lkunelk/hopping-eggplant/hardware/results/sample_sim.png

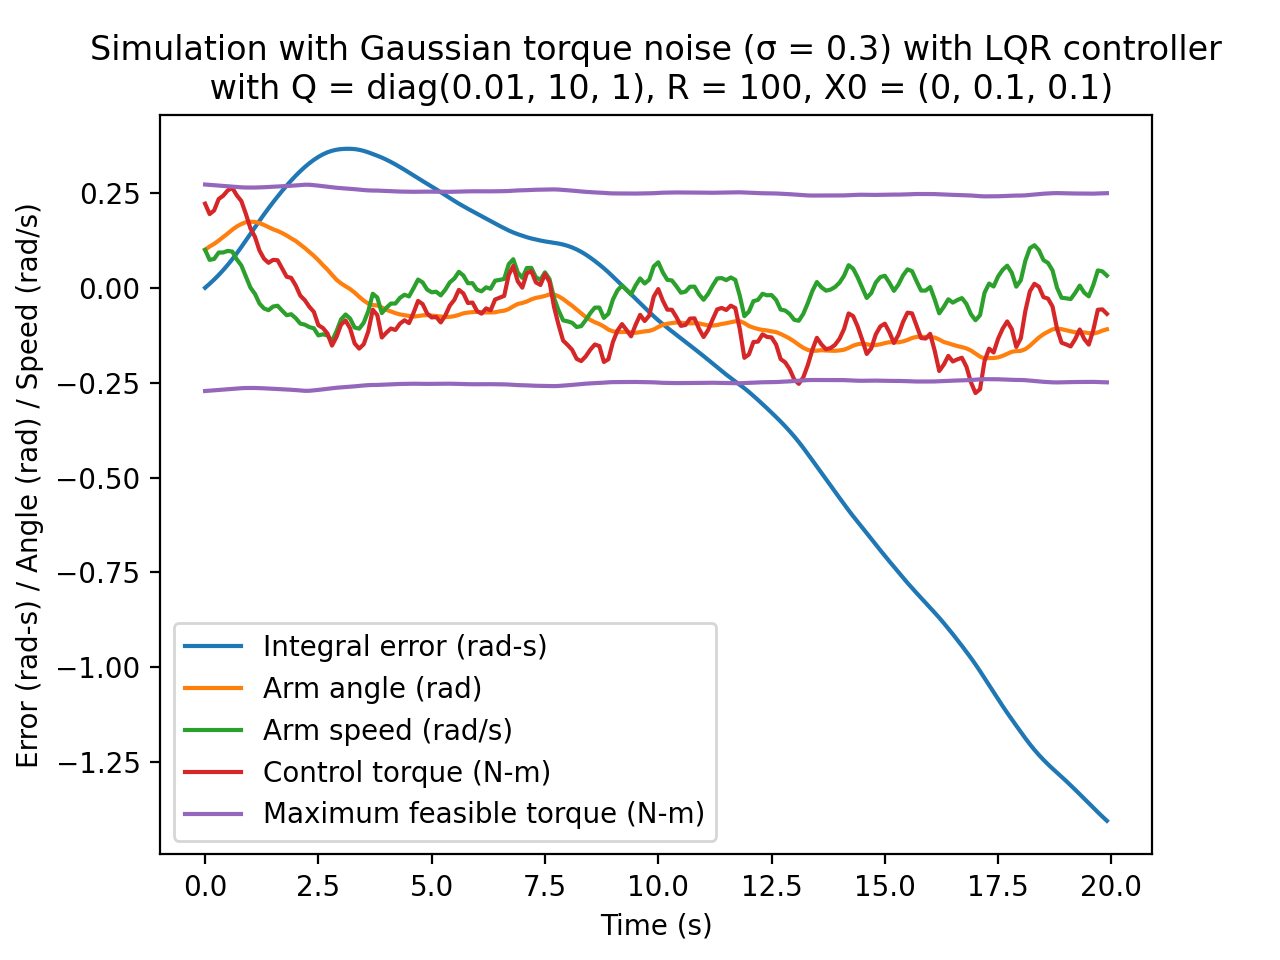
hardware/results/sample_sim.png
