lkunelk/hopping-eggplant/hardware/results/sample_sim_0p1sig.png

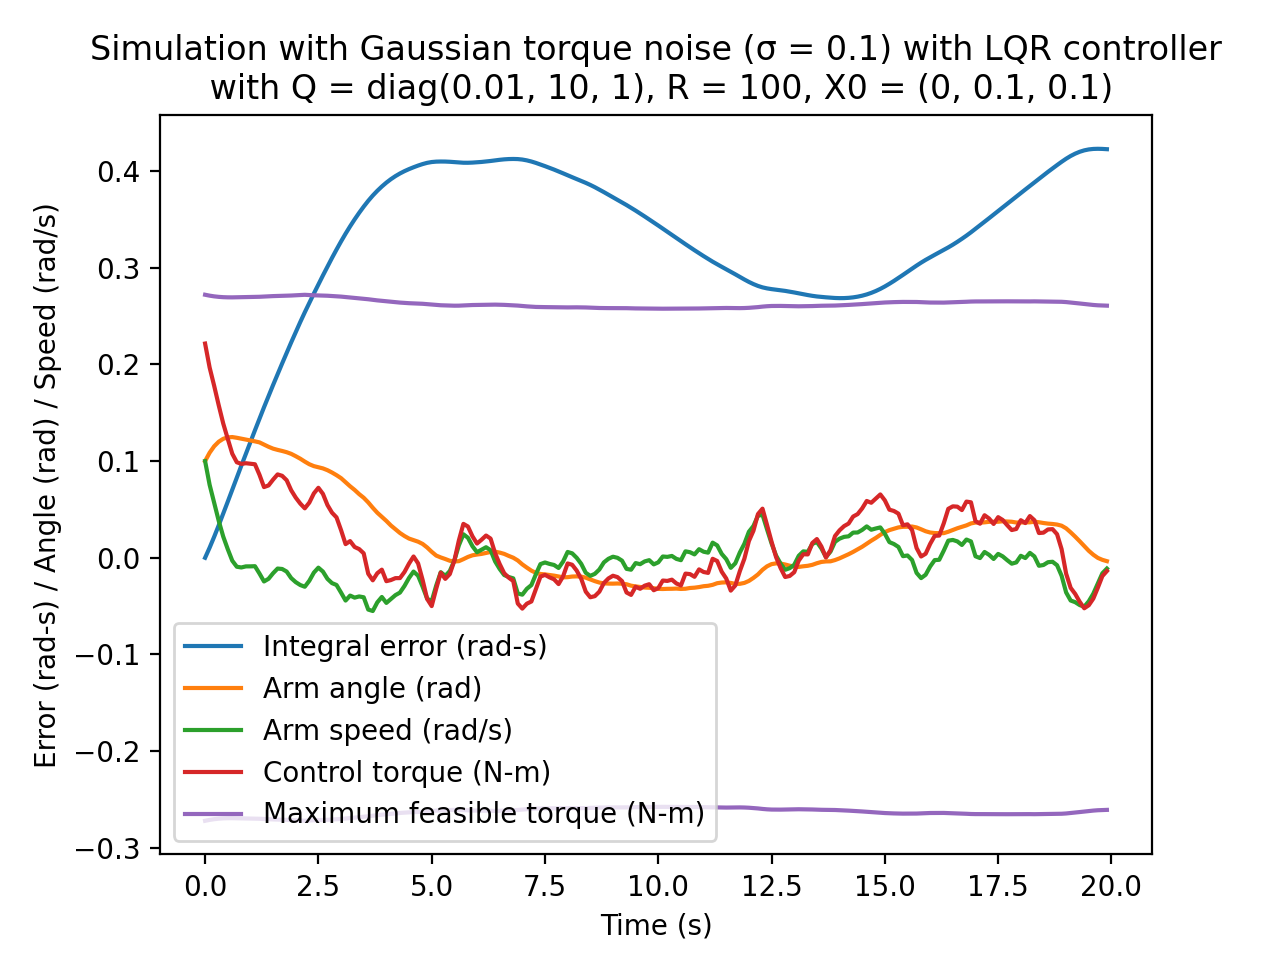
hardware/results/sample_sim_0p1sig.png
