lkunelk/hopping-eggplant/hardware/results/sample_sim_0p1sig_fly_speed.png

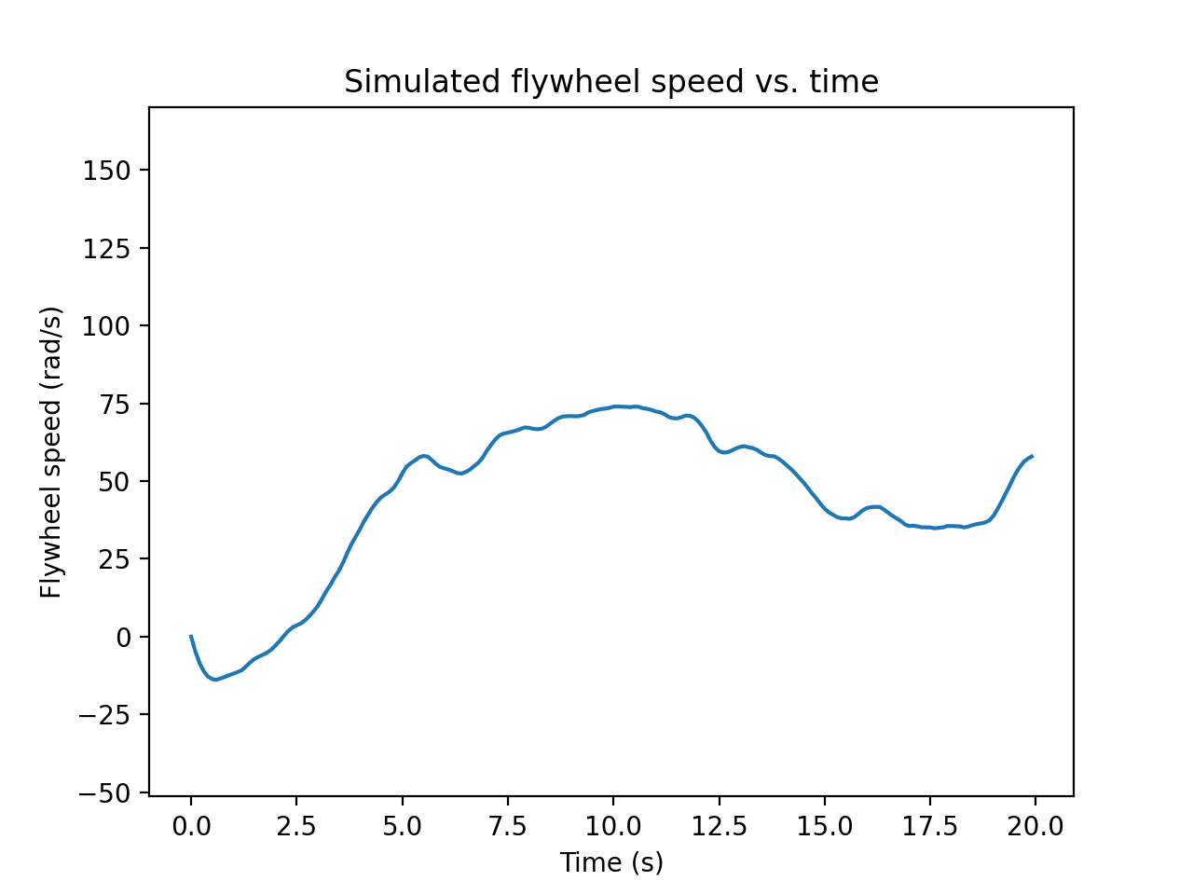
hardware/results/sample_sim_0p1sig_fly_speed.png
