lkunelk/hopping-eggplant/hardware/results/sample_sim_0p4sig_0p4s_delay.png

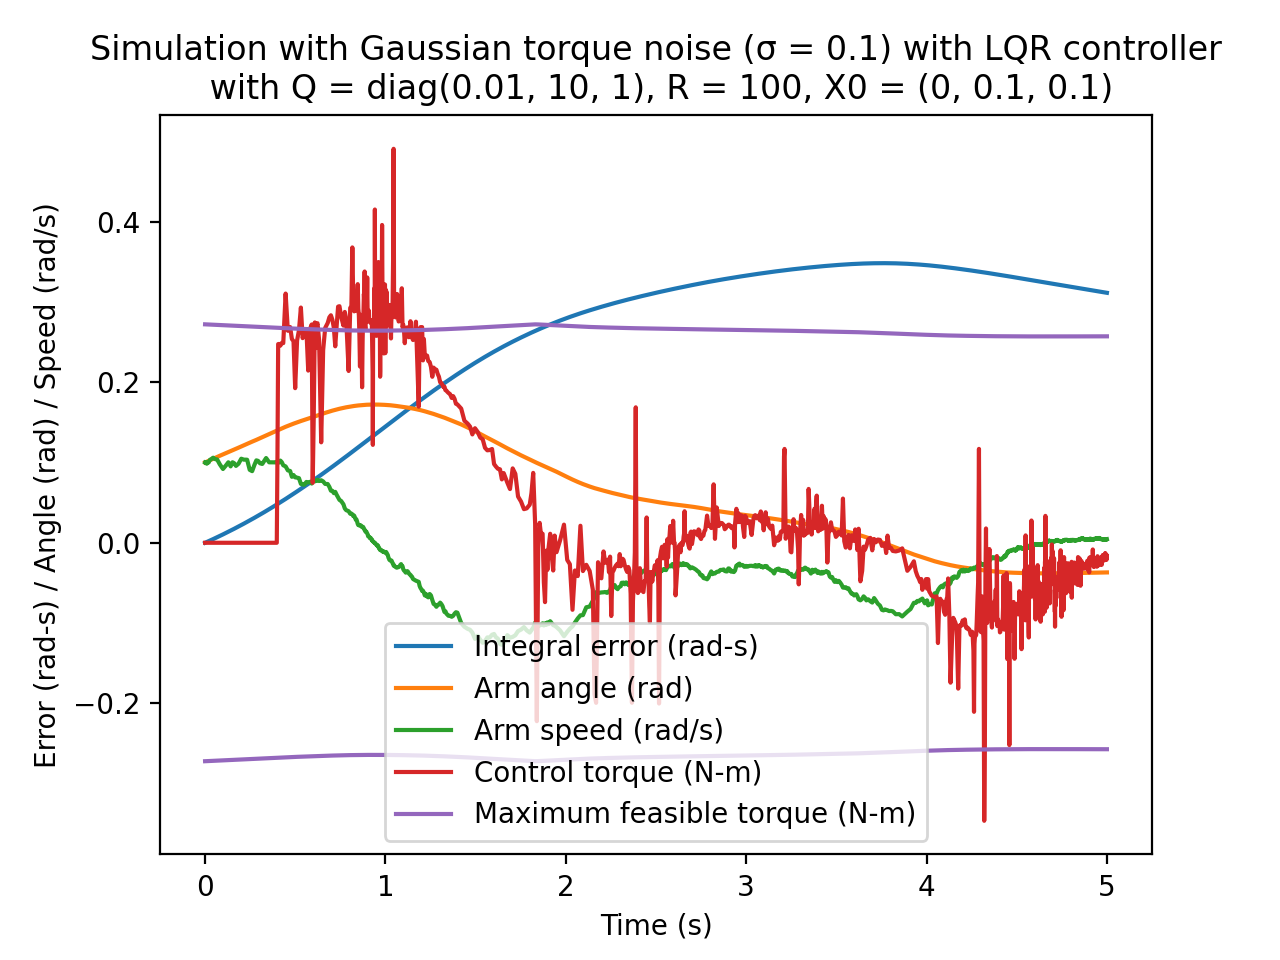
hardware/results/sample_sim_0p4sig_0p4s_delay.png
