lkunelk/hopping-eggplant/hardware/results/sample_sim_0p4sig_0p4s_delay_fly_speed.png

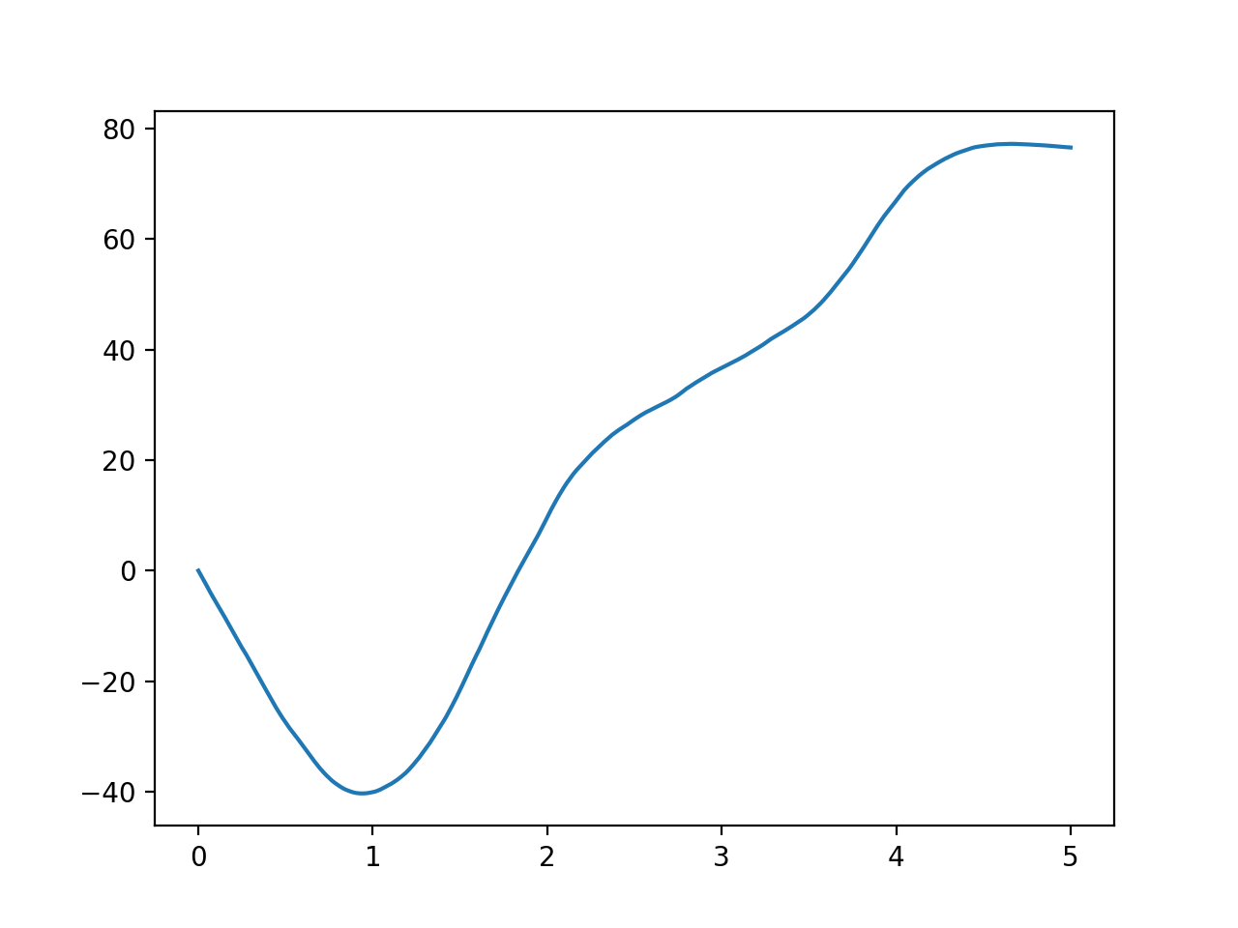
hardware/results/sample_sim_0p4sig_0p4s_delay_fly_speed.png
