lkunelk/hopping-eggplant/hardware/results/sample_sim_fly_speed.png

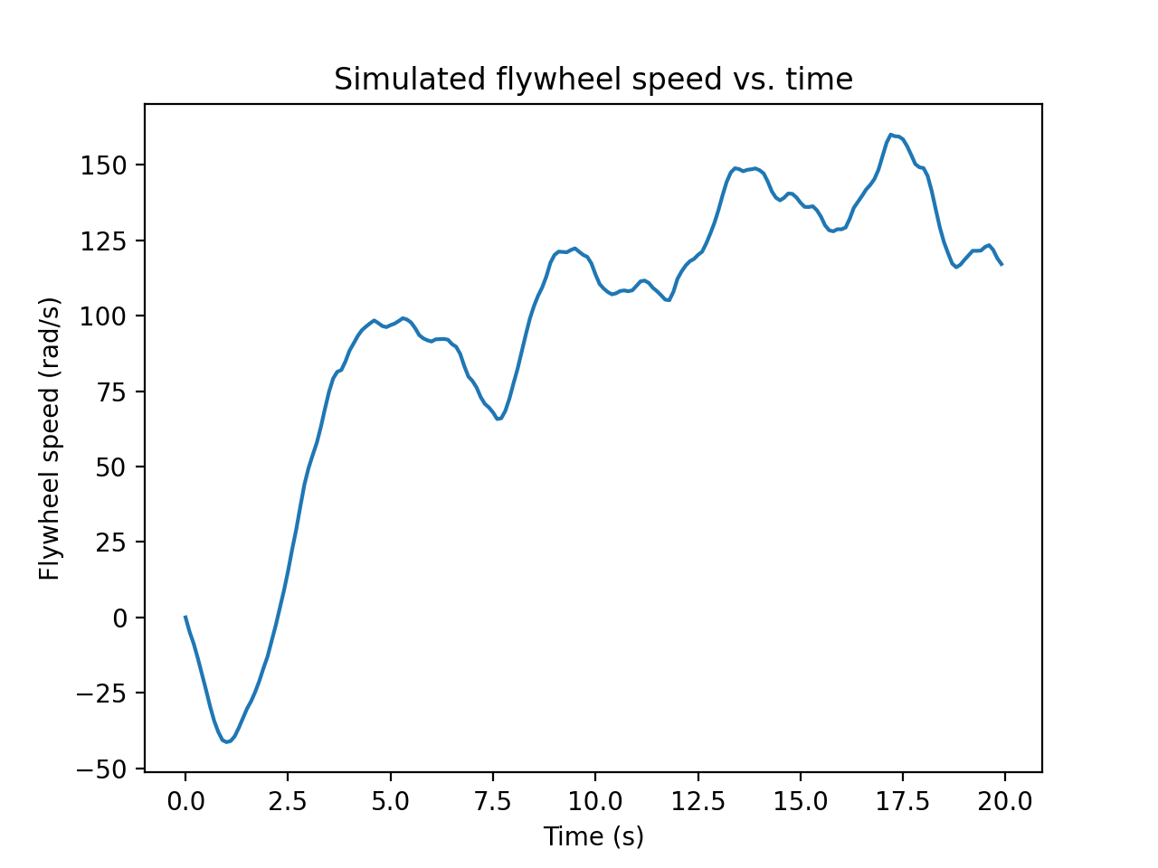
hardware/results/sample_sim_fly_speed.png
