lkunelk/hopping-eggplant/hardware/stwork/g431_test/g431_test.ioc

Mcu.UserName=STM32G431CBUx
PB14.GPIO_Label=Temperature
PA0.GPIO_Label=VBUS
PC6.GPIO_Label=STATUS
PB6.GPIO_Label=A
PB11.Signal=GPIO_Input
PB13.Signal=OPAMP3_VINP
PB15.Signal=TIM1_CH3N
PA15.GPIO_Label=PWMIN
PA12.Signal=TIM1_CH2N
PB6.Signal=S_TIM4_CH1
PB2.Signal=OPAMP3_VINM
PB12.GPIO_Label=POT
PC4.GPIO_Label=BEMF2
PB7.Signal=S_TIM4_CH2
PA8.Signal=S_TIM1_CH1
PA0.Signal=SharedAnalog_PA0
PB7.GPIO_Label=B
PB1.Signal=OPAMP3_VOUT
PA6.Signal=OPAMP2_VOUT
PA10.Signal=S_TIM1_CH3
PA15.Signal=GPXTI15
PB8-BOOT0.GPIO_Label=Z
PB5.GPIO_Label=GPIO_BEMF
PA4.GPIO_Label=BEMF1
PF1-OSC_OUT.Signal=RCC_OSC_OUT
PB4.Signal=USART2_RX
PA3.Signal=OPAMP1_VINM
PC13.Signal=TIM1_CH1N
PC4.Signal=GPIO_Input
PC6.Signal=GPIO_Output
PB11.GPIO_Label=BEMF3
PA13.Signal=SYS_JTMS-SWDIO
PA9.Signal=S_TIM1_CH2
PA1.Signal=OPAMP1_VINP
PB14.Signal=GPIO_Analog
PA5.Signal=OPAMP2_VINM
PB8-BOOT0.Signal=GPXTI8
PA2.Signal=OPAMP1_VOUT
PB3.Signal=USART2_TX
PA4.Signal=GPIO_Input
PB5.Signal=GPIO_Output
PA14.Signal=SYS_JTCK-SWCLK
PF0-OSC_IN.Signal=RCC_OSC_IN
PB0.Signal=ADC1_IN15
PB12.Signal=SharedAnalog_PB12
PA7.Signal=OPAMP2_VINP
