lkunelk/hopping-eggplant/hardware/stwork/g431_test/Inc/main.h

#define CTRL0 220
#define VBUS_Pin GPIO_PIN_0
#define VBUS_GPIO_Port GPIOA
#define BEMF1_Pin GPIO_PIN_4
#define BEMF1_GPIO_Port GPIOA
#define BEMF2_Pin GPIO_PIN_4
#define BEMF2_GPIO_Port GPIOC
#define BEMF3_Pin GPIO_PIN_11
#define BEMF3_GPIO_Port GPIOB
#define POT_Pin GPIO_PIN_12
#define POT_GPIO_Port GPIOB
#define Temperature_Pin GPIO_PIN_14
#define Temperature_GPIO_Port GPIOB
#define STATUS_Pin GPIO_PIN_6
#define STATUS_GPIO_Port GPIOC
#define PWMIN_Pin GPIO_PIN_15
#define PWMIN_GPIO_Port GPIOA
#define PWMIN_EXTI_IRQn EXTI15_10_IRQn
#define GPIO_BEMF_Pin GPIO_PIN_5
#define GPIO_BEMF_GPIO_Port GPIOB
#define A_Pin GPIO_PIN_6
#define A_GPIO_Port GPIOB
#define B_Pin GPIO_PIN_7
#define B_GPIO_Port GPIOB
#define Z_Pin GPIO_PIN_8
#define Z_GPIO_Port GPIOB
#define Z_EXTI_IRQn EXTI9_5_IRQn
#define UART_RX_INACTIVITY_TIMEOUT 1000
